pikvm/pikvm/docs/arduino_hid.md

!!! warning "Legacy warning"
    This page describes the legacy keyboard and mouse emulator used in old DIY builds.
    There is no point using it today because there is a more modern and better replacement for the [new Pico HID](pico_hid.md).
    This one can also serve as an in-place compatible replacement for the Arduino HID in the old build.

-----
## Serial HID

!!! warning "PiKVM V3 note"
    Use [the SPI HID](#spi-hid) for V3. Otherwise, you won't be able to use the Serial console.

### USB keyboard and mouse

1. ??? example "Get some parts"
    * Arduino Pro Micro (based on an ATMega32u4).
    * [Logic level shifter](https://www.sparkfun.com/products/12009).
    * 1x NPN transistor (almost any NPN transistor: 2n2222 or similar).
    * 1x 390 Ohm resistor.
    * A breadboard and wires.

2. ??? example "Build the Arduino HID according to the scheme"
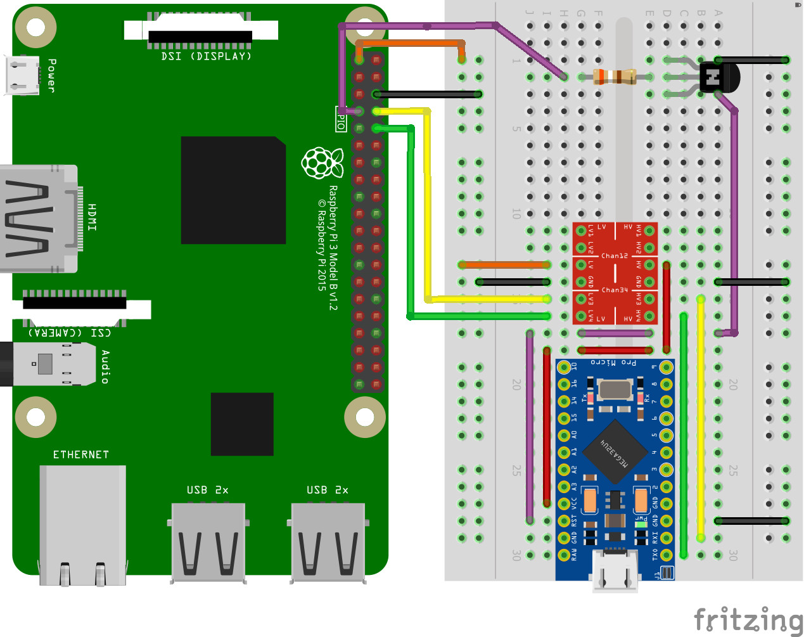
[picture p38: docs/arduino_hid/arduino_serial_hid.jpg]
    

3. Power up PiKVM and switch it to RW-mode using command `rw`.

4. Add these lines to `/etc/kvmd/override.yaml`:

    ```yaml
    kvmd:
        hid:
            type: serial
            reset_pin: 4
            device: /dev/kvmd-hid
    ```

5. Create file `/etc/udev/rules.d/99-kvmd-extra.rules`:

    ```udev
    KERNEL=="ttyAMA0", SYMLINK+="kvmd-hid"
    ```

6. Run `systemctl disable getty@ttyAMA0.service`.

7. Remove `console=ttyAMA0,115200`or `console=serial0,115200` and `kgdboc=ttyAMA0,115200` or `kgdboc=serial0,115200` from `/boot/cmdline.txt`.

8. [Flash the Arduino HID](flashing_hid.md).

9. Perform `reboot`.

### PS/2 keyboard

Using the PS/2 firmware currently have some limitations:

* The possibility of using the switchable USB HID is excluded.
* PS/2 mouse is not supported right now (but it will).

Both of these problems will be solved in the nearest future and the two different firmware versions will be combined into one universal one.

To select the PS/2 firmware, follow the instructions for the [USB](#usb-keyboard-and-mouse), but with one exception:

??? note "Before `make` you will need to edit file `platformio-avr.ini`"
    Open the file and find these lines:

    ```ini
    [_common]
    build_flags =
        -DHID_PS2_KBD_CLOCK_PIN=7
        -DHID_PS2_KBD_DATA_PIN=5
        -DHID_USB_CHECK_ENDPOINT
    # ----- The default config with dynamic switching -----
        -DHID_DYNAMIC
        -DHID_WITH_USB
        -DHID_SET_USB_KBD
        -DHID_SET_USB_MOUSE_ABS
    # ----- PS2 keyboard only -----
    #   -DHID_WITH_PS2
    #   -DHID_SET_PS2_KBD
    # ----- PS2 keyboard + USB absolute mouse -----
    #   -DHID_WITH_USB
    #   -DHID_WITH_PS2
    #   -DHID_SET_PS2_KBD
    #   -DHID_SET_USB_MOUSE_ABS
    # ----- PS2 keyboard + USB relative mouse -----
    #   -DHID_WITH_USB
    #   -DHID_WITH_PS2
    #   -DHID_SET_PS2_KBD
    #   -DHID_SET_USB_MOUSE_REL
    ```

    By default, the firmware works with USB HID and supports dynamic mode switching. You can choose one of the other modes by commenting some lines and uncommenting others. This example to use a USB mouse and PS/2 keyboard:

    ```ini
    ...
    # ----- The default config with dynamic switching -----
    #   -DHID_DYNAMIC
    #   -DHID_WITH_USB
    #   -DHID_SET_USB_KBD
    #   -DHID_SET_USB_MOUSE_ABS
    # ----- PS2 keyboard only -----
    ...
    # ----- PS2 keyboard + USB absolute mouse -----
        -DHID_WITH_USB
        -DHID_WITH_PS2
        -DHID_SET_PS2_KBD
        -DHID_SET_USB_MOUSE_ABS
    # ----- PS2 keyboard + USB relative mouse -----
    ...
    ```

Next, connect Arduino pins to the female PS/2 port of your motherboard. Choose the purple port. If your motherboard only have one port, it's probably universal and can be used either for the keyboard or for the mouse. Most likely, it is painted in two colors: green and purple. You can use it either.

??? example "Follow the diagram"
    | Female PS/2 port (front view) | Pinout |
    |-------------------------------|--------|
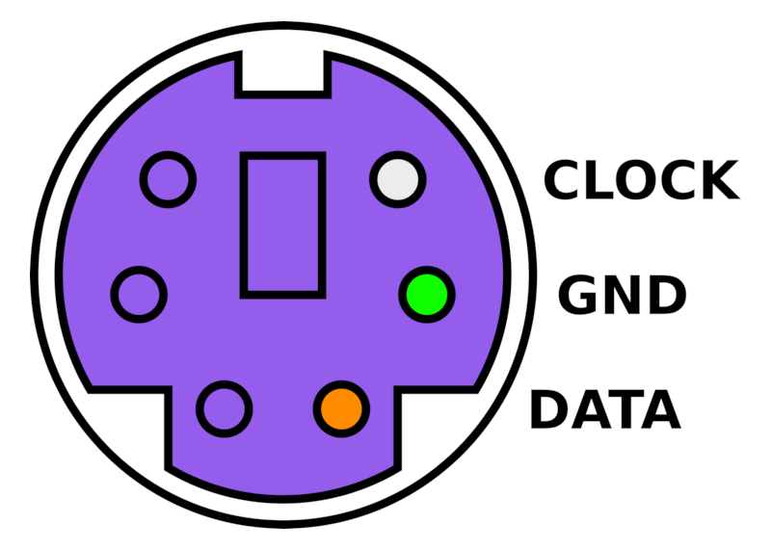
[picture p39: docs/arduino_hid/ps2_kbd.png]
    |  | Arduino pin 7 <-> PS/2 CLOCK<br>Arduino pin 5 <-> PS/2 DATA<br>Arduino GND pin <-> PS/2 GND |

    !!! warning
        Connect VIN pin of Arduino to [any Raspberry's 5v pin](https://pinout.xyz/pinout/5v_power) for PS/2 only device. But you don't need to connect the Arduino VIN pin if you connected USB (Arduino will get power through it).

-----
## SPI HID

Using an SPI connection, an Arduino Micro (not Pro) or compatible can be flashed from the Pi and used as an HID keyboard and mouse. Unlike UART, SPI does not share pins with Bluetooth on the Raspberry Pi so the Bluetooth radio does not need to be disabled.

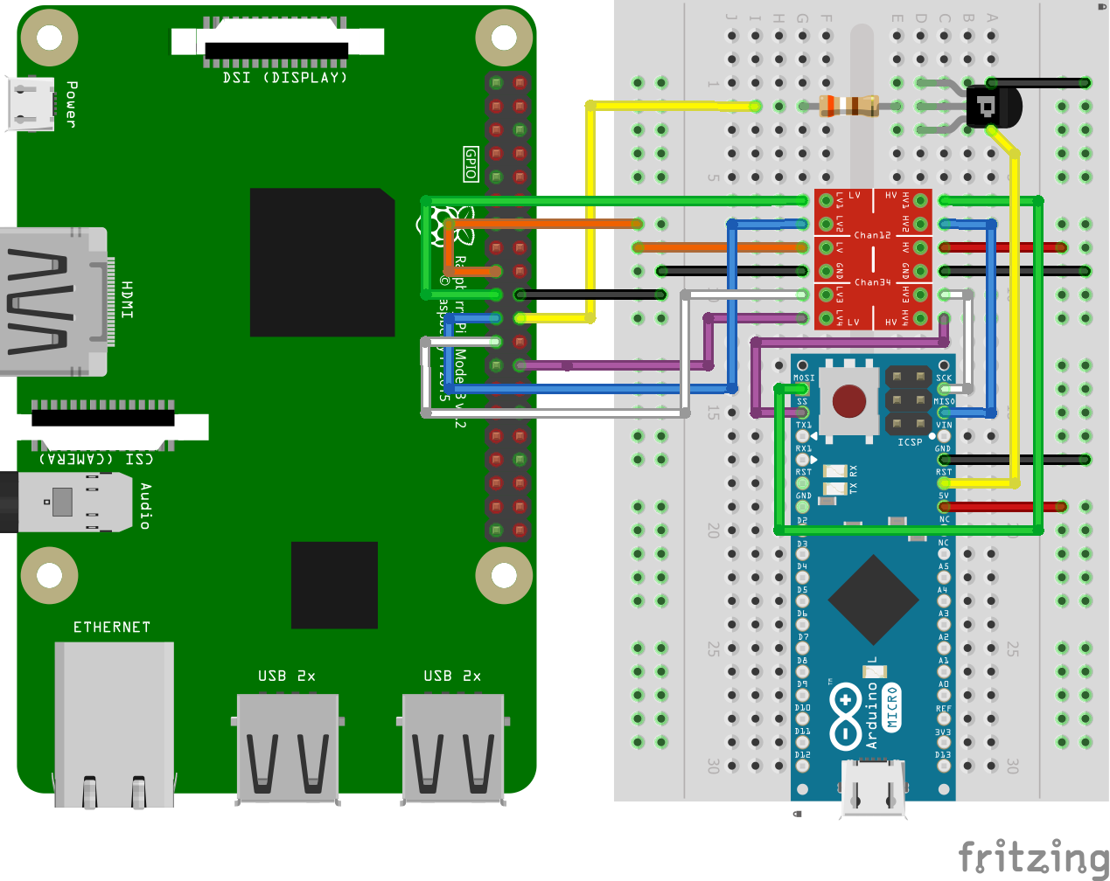
[picture p40: docs/arduino_hid/arduino_spi_hid.png]
Diagram of the Arduino SPI wiring for HID keyboard and mouse.


Before powering either device, double-check the connections. The following should be wired from the Pi to either the level shifter or the Arduino. While the Arduino tolerates 3.3V logic input, 5V outputs from the Arduino can damage or destroy the Raspberry Pi and must not be connected directly to 3.3V GPIO pins directly.

### Parts list

There are very few parts needed besides the Raspberry Pi to build the solution. Some parts may be purchased with or without headers, if headers are not pre-soldered, it may be necessary to order some breakaway header strips and solder them to the boards prior to assembly unless the wires will be soldered directly to the boards.

* Raspberry Pi Zero W or Pi 4 are the most popular boards for this solution, pre-soldered headers recommended
* Arduino Micro (or compatible) microcontroller board with pre-soldered headers recommended
* Logic Level Converter. This may be RX/TX, Bidirectional, or Single Supply
* 1x PNP transistor (2n2907 or equivalent).  Note this is different from the one suggested in the Serial HID docs above, that is an NPN while this is a PNP.
* 1x 390 ohm resistor
* Dupont wires (female to male pin) recommended for breadboard or other suitable means of making the connections
* *Optional:* Breakaway headers for the logic level converter
* *Optional:* Breadboard large enough to accommodate the parts
* *Optional:* Header pins for connection to a breadboard

!!! note
    A smaller "Pro Micro" board is available in a 3.3V model but the SS connection (RX_LED) is not available as a separate pin or solderable hole. If using this board, a jumper wire can be soldered to the resistor for the RX_LED but there is risk of burning the resistor, the LED, the board, or other components in the process. Advantages of this board include not requiring a logic level converter and reduced breadboard or board space for building the solution.

### List of connections to be made

For the primary functionality, most connections are made using a 4-channel bidirectional level shifter

* Pi 3v3 to LV on the level shifter
* Pi Ground to LV GND
* Arduino GND to HV GND
* GPIO10 (MOSI) via the level shifter to MOSI on the Arduino
* GPIO9 (MISO) via the level shifter to MISO on the Arduino
* GPIO11 (SPIO_SCLK) via the level shifter to SCK on the Arduino
* GPIO7 (SPIO_CE1_N) via the level shifter to SS (or RX_LED) on the Arduino

An additional circuit is used with a transistor to reset the HID for mode changes and for SPI programming as follows:

* GPIO25 to PNP base on transistor
* PNP emitter to ground
* PNP collector to  RST on the Arduino

Pictures of this setup are also available in full resolution for download to assist for both the Raspberry Pi and the Arduino board. A smaller version of the images has been included on this page and can be downloaded.

| Raspberry Pi Closeup | Breadboard with Arduino |
|---|---|
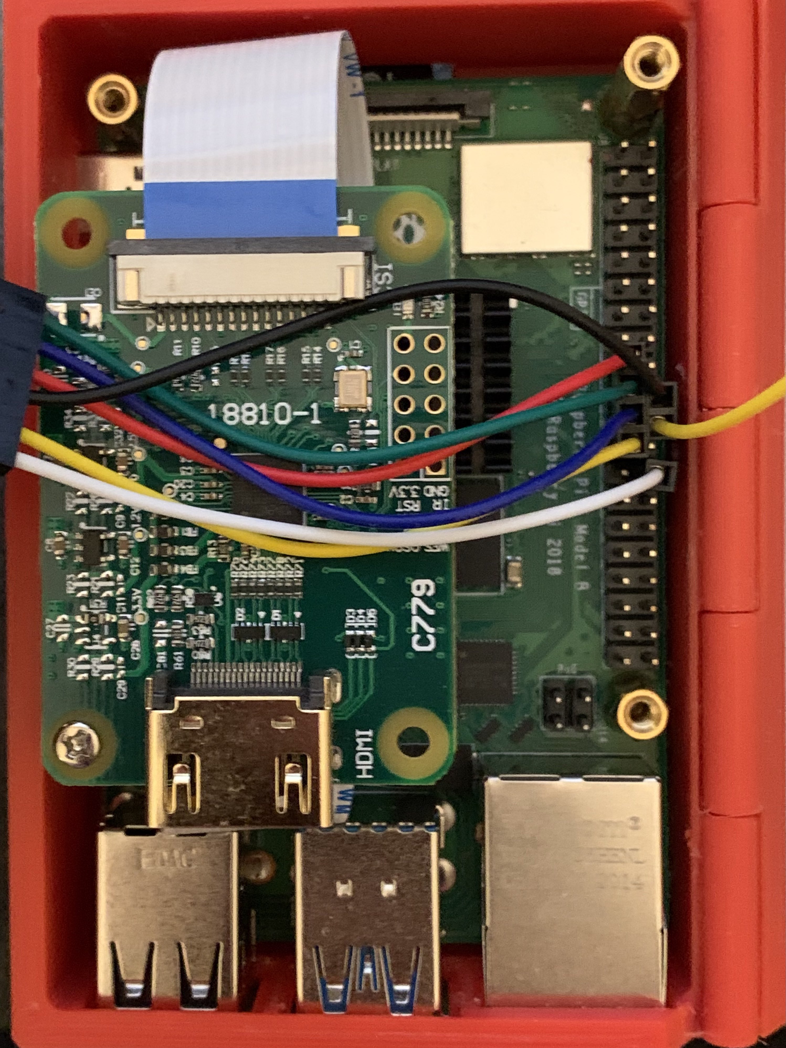
[picture p41: docs/arduino_hid/arduino_spi_hid_rpi.jpg]
A closeup of the Raspberry Pi wired to the breadboard.
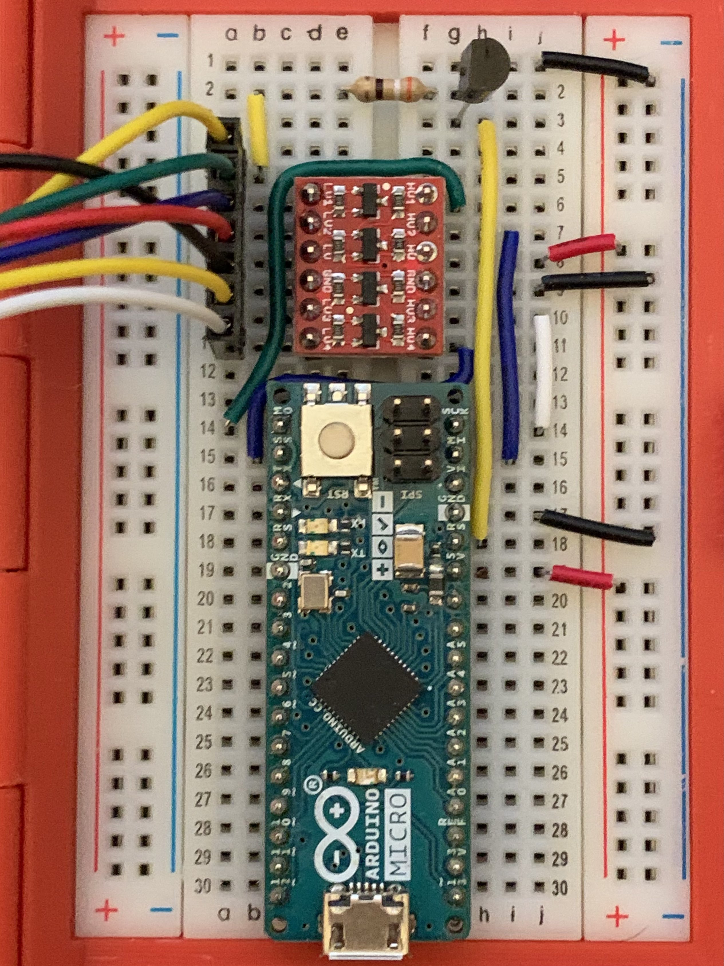
[picture p42: docs/arduino_hid/arduino_spi_hid_bb.jpg]
Arduino on a breadboard fully wired to the Pi.
|  |  |

Programming assumes the Arduino is powered via USB, either from the connected host or the Pi itself. If the USB is not connected, 5 V may be provided by the Raspberry Pi GPIO but should be disconnected prior to connecting USB to the Arduino's USB port. The Raspberry Pi does not have backcurrent protection, a circuit using one or more Schottky diodes can be built to OR power from multiple sources but it's easier and more cost effective to avoid conflict and voltage differences between power supplies by leaving the 5 V wire disconnected.

### Preparing the installation for SPI devices and programming

As of the latest package release, the kvmd service supports SPI. It should be sufficient to ensure the packages are up-to-date with the latest release, the programmer is installed, and the SPI device overlay is loaded at boot.

* Switch the filesystem to read-write mode with `rw`
* Add `dtoverlay=spi0-1cs` to `/boot/config.txt`
* Perform `reboot`.

### Flashing the Arduino

Instructions on flashing the Arduino can be found on the page [Flash the Arduino HID](flashing_hid.md).

If programming fails, ensure the Arduino is powered and check the wiring again. If there is a misconfiguration, power off the Pi and the Arduino, correct the wiring, and try again. Note it is not recommended or required to supply 5V power from the Raspberry Pi if the Arduino is USB powered, if the issue appears to be power related it may be removed from the solution and replaced with a powered USB connection if it will aid in troubleshooting but check all other wires first to ensure there are no shorts.

After you have double and triple-checked your wiring (in particular make sure the pins you are using on the Pi are correct, the documentation uses the GPIO pin labels, NOT the sequential pin numbers from 1-40. A good pinout reference is [@Gadgetoid's version](https://pinout.xyz/#), you might try flashing the Arduino by holding down the RESET button on the chip while running `make install`.  If this works, then at least you know your SPI wiring is correct.

Wiring problems are a common issue but there could be other reasons for programming not to complete. While it is not possible to list every possible problem and solution here, there is an active [user community](https://pikvm.org/support/) with others familiar with the solution and willing to help.

### Enable the SPI configuration and restart kvmd

Once the installation has completed, all that should remain is to add the following configuration to `/etc/kvmd/override.yaml` and restart the kvmd service. If the first line exists due to existing overrides, omit that line and either add or update the hid section as appropriate.

```yaml
kvmd:
    hid:
        type: spi
        chip: 0
        bus: 0
        sw_cs_pin: 7
        reset_pin: 25
        reset_inverted: true
```

After saving the changes to `/etc/kvmd/override.yaml`, restart `kvmd` and clear your browser cache. The command to restart `kvmd` is

```
# systemctl restart kvmd
```

If your device is still in read-write mode, `ro` will put the SD back in read-only mode.

-----
## Fixing the USB absolute mouse on Windows 98

Due to an ancient buggy driver, the USB absolute mouse on Windows 98 moves only within the upper-left quarter of the screen. To fix this, just recompile the firmware with uncommented flag `-DHID_WITH_USB_WIN98` in `platformio-avr.ini`.
