pikvm/pikvm/docs/blog/posts/2020/2020-08-02/index.md

---
title: "Ready-made images for Raspberry Pi4"
date: 2020-08-02
slug: ready-made-images-for-raspberry-pi4
description: >
      Now we provide the ready-made images for Raspberry Pi 4. You no longer need to build OS manually!
categories:
    - Products
authors:
    - mdevaev
links:
    - PiKVM: https://pikvm.org
    - Discord: https://discord.gg/bpmXfz
comments: true
---

The big update! Now we provide the ready-made images for Raspberry Pi 4. You no longer need to build OS manually!

<!-- more -->

You can flash the Pi-KVM OS to SD card under Linux, Mac, and Windows using the graphical installer.

Downloads are here: https://pikvm.org/download/.

The manual is here: https://docs.pikvm.org/flashing_os/.

Oh, and as you can see, now we have a small website: https://pikvm.org/. I would appreciate it if you share this link with your colleagues or friends in social networks.
