pikvm/pikvm/docs/index.md

---
title: PiKVM Handbook
description: Comprehensive guide to configuring and using your PiKVM
---

**Welcome to the [PiKVM](https://pikvm.org) Handbook**—a complete
documentation of the Open-Source KVM-over-IP on Raspberry Pi!

Here you will find comprehensive information about all aspects of the
operation of PiKVM, get answers to your most difficult questions and be
able to solve the problems that have arisen.

## Where to start?

* Check out the **device instructions**:

    {!_device_guides.md!}

* Learn about the **[basics of working with PiKVM](cheatsheet.md)**.

* **Explore the features of PiKVM** using the site's table of contents.

* **If you encounter a problem**, take a look at the **[FAQ](faq.md)**, but if nothing helped,
  feel free to contact our **[Support](https://pikvm.org/support/)** - many of experienced users and the PiKVM team will definitely help you.

## Links

* Website: **https://pikvm.org**
* GitHub: **https://github.com/pikvm**
* Discord: 
* Reddit: 
* [Forum](https://forum.pishop.com/c/pikvm)
