pikvm/pikvm/docs/blog/posts/2022/2022-06-09/index.md

---
title: "KVMD 3.101: PiKVM V3 + Audio = ❤️"
date: 2022-06-09
slug: kvmd-3-101-audio-on-pikvm-v3
description: >
    We are finally ready to provide audio for testing by all V3 users
categories:
    - Releases
authors:
    - mdevaev
links:
    - PiKVM: https://pikvm.org
    - Discord: https://discord.gg/bpmXfz5
    - KVMD release: https://github.com/pikvm/kvmd/releases/tag/v3.101
comments: true
---

This moment has come! We are finally ready to provide audio for testing by all V3 users. 

<!-- more -->

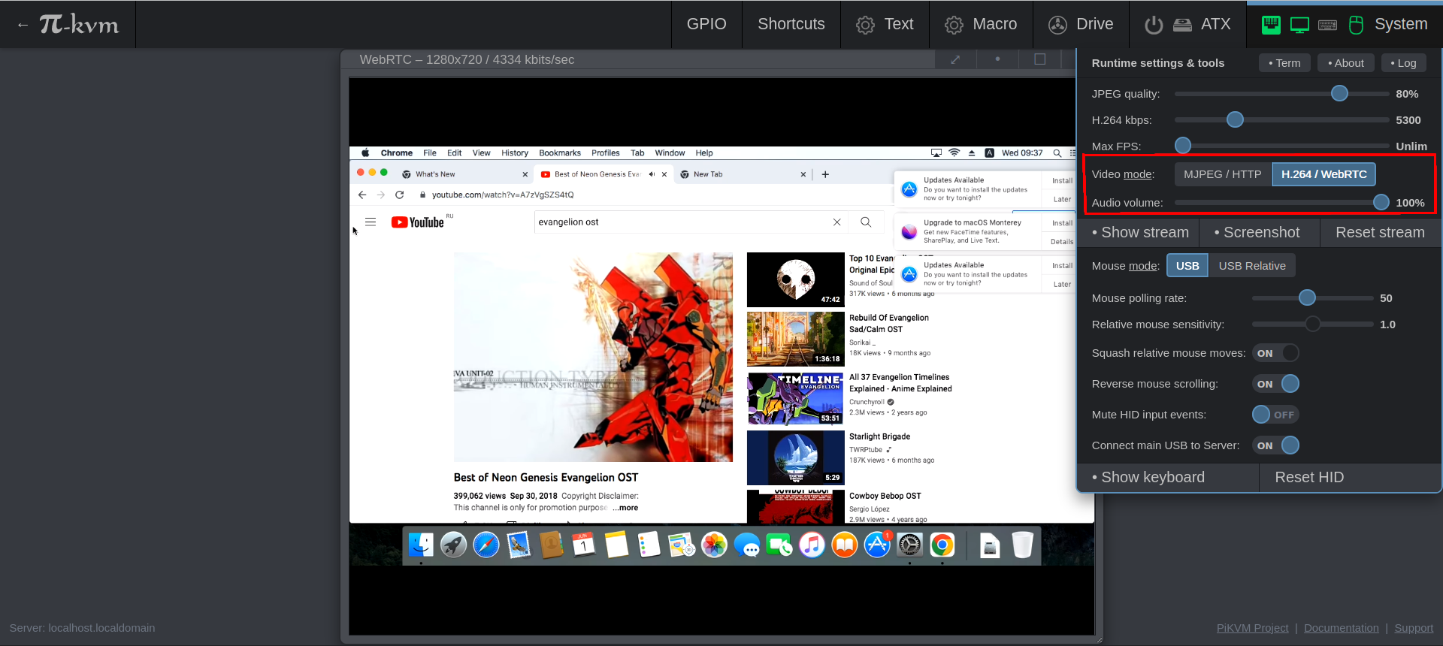
[picture p112: docs/blog/posts/2022/2022-06-09/pikvm-v3-audio.webp]
Audio on PiKVM v3


Right now everything is working pretty stable, so if you really wanted to watch a movie on KVM or something like that—this is your chance!

To start using audio, follow the simple instructions here: https://docs.pikvm.org/audio.
