pikvm/pikvm/docs/blog/posts/2024/2024-08-19/index.md

---
title: "KVMD 4.4: HDMI passthrough on V4 Plus is stable now"
date: 2024-08-19
slug: kvmd-4-4-stable-hdmi-passthrough-on-v4-plus
description: >
    Thanks to the work of the Raspberry kernel team, a bug related to incorrect colors in H.264 was finally fixed while working with passthrough
categories:
    - Products
authors:
    - mdevaev
links:
    - PiKVM: https://pikvm.org
    - Discord: https://discord.gg/bpmXfz5
    - KVMD release: https://github.com/pikvm/kvmd/releases/tag/v4.4
comments: true
---

Thanks to the work of the Raspberry kernel team, a bug related to incorrect colors in H.264 was finally fixed while working with passthrough.

<!-- more -->

With the new release, this feature is now enabled by default, and you will get great juicy colors both in the stream and on the external physical monitor. See [the documentation](https://docs.pikvm.org/pass) for details on setting this up.

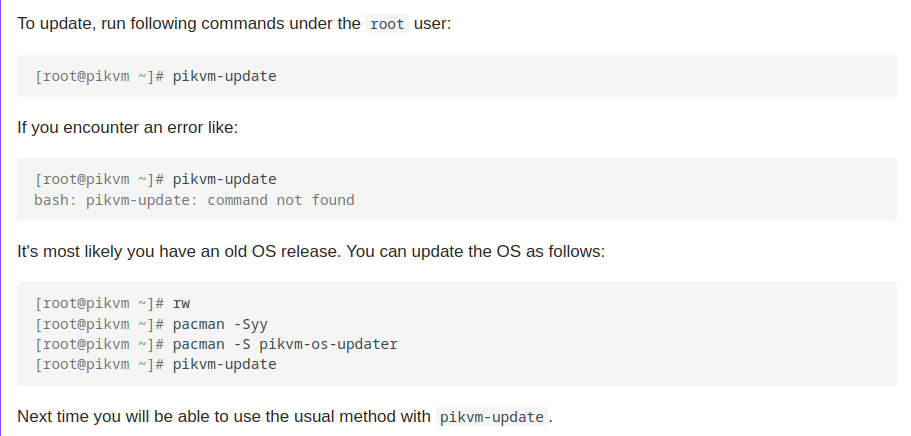
[picture p115: docs/blog/posts/2024/2024-08-19/pikvm-os-update.webp]
Updating PiKVM OS
