pikvm/pikvm/docs/blog/posts/2025/2025-01-24/index.md

---
title: "KVMD 4.49: DVD images support"
date: 2025-01-24
slug: kvmd-4-49-dvd-images-support
description: >
    Starting with KVMD 4.49, the old 2.2 GB CD limit was removed
categories:
    - Releases
authors:
    - mdevaev
links:
    - PiKVM: https://pikvm.org
    - Discord: https://discord.gg/bpmXfz5
    - KVMD release: https://github.com/pikvm/kvmd/releases/tag/v4.49
comments: true
---

Starting with KVMD 4.49, **the old 2.2 GB CD limit is now removed**.

<!-- more -->

PiKVM just learned how to support large DVD images natively, which means that **you no longer need Ventoy to prepare Flash images for PiKVM**. You can even use the official Windows ISO to install the OS! Small ISO images will be handled as CD as before, but for big images PiKVM will switch emulation to DVD mode automatically.

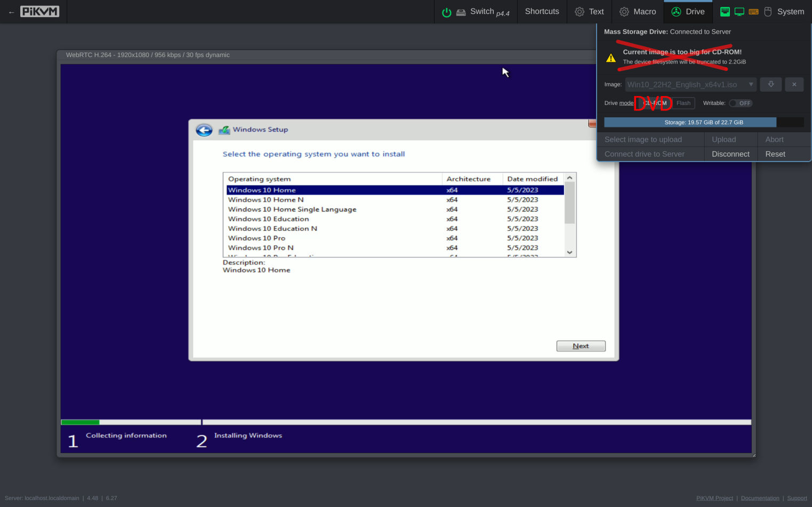
[picture p117: docs/blog/posts/2025/2025-01-24/no-cd-iso-limit.webp]
No CD ISO limit


How to update: `pikvm-update`, as usual.

If you've been dreaming of getting DVD emulation, then your wish has been fulfilled 🙂
