pikvm/pikvm/docs/blog/posts/2025/2025-05-27/index.md

---
title: "KVMD 4.76: Advanced diagnostics for the video stream"
date: 2025-05-27
slug: kvmd-4-76-advanced-diagnostics-for-the-video-streams
description: >
    Now you will see the reason why there is no signal
categories:
    - Releases
authors:
    - mdevaev
links:
    - PiKVM: https://pikvm.org
    - Discord: https://discord.gg/bpmXfz5
    - KVMD release: https://github.com/pikvm/kvmd/releases/tag/v4.76
comments: true
---

Now you will see the reason why there is no signal. We reliably distinguish the condition of the cable from the absence of a signal or unsupported video mode.

<!-- more -->

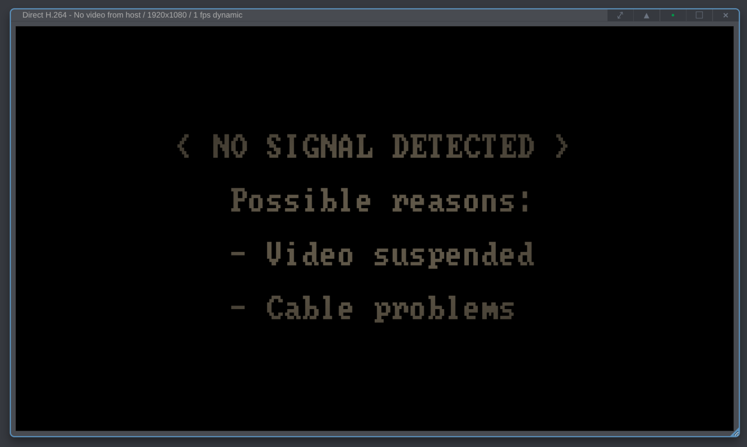
[picture p118: docs/blog/posts/2025/2025-05-27/video-stream-diagnostics.webp]
Video stream diagnostics
