pikvm/pikvm/docs/switch/switch_back.jpg

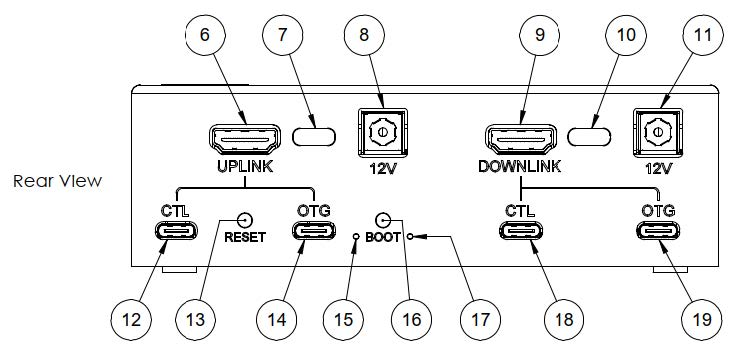
docs/switch/switch_back.jpg
