pikvm/pikvm/docs/switch/switch_back_blank.jpg

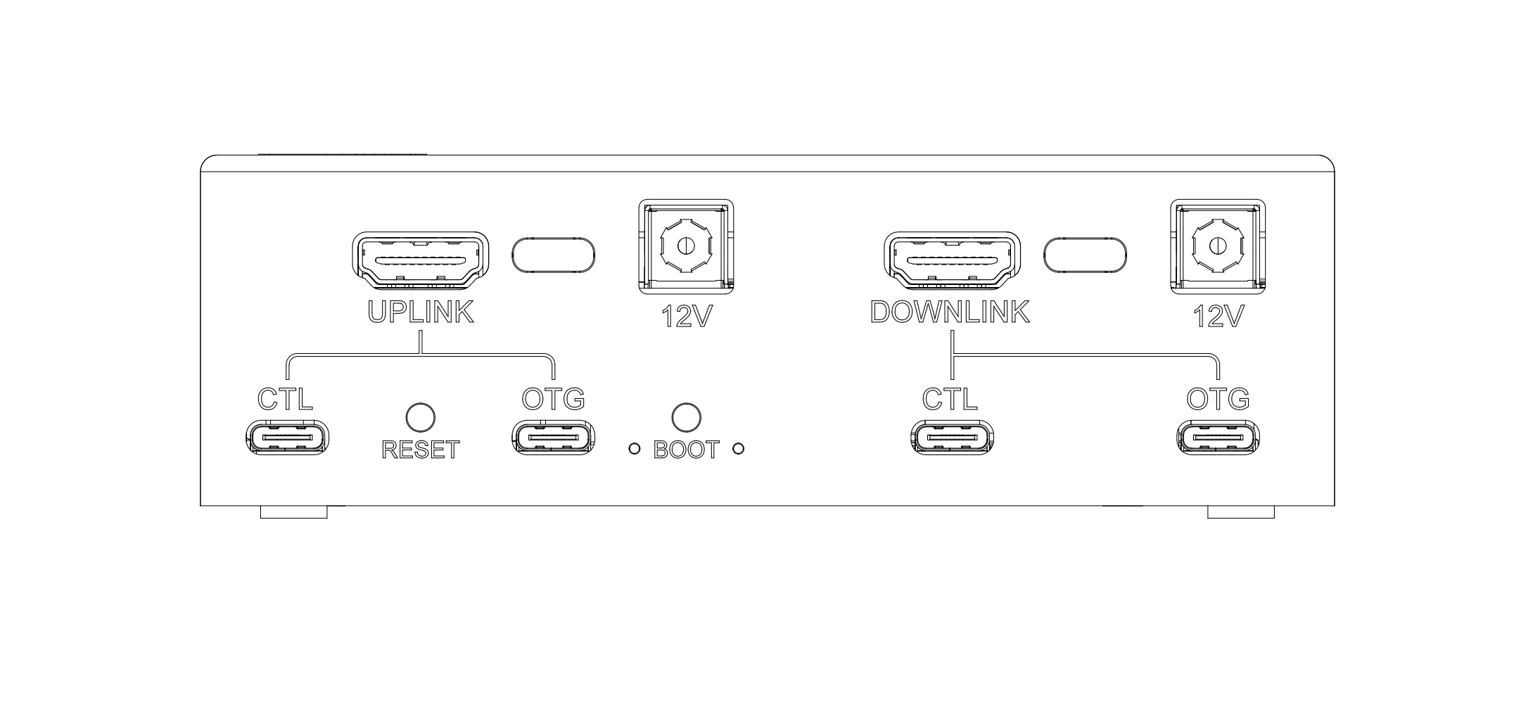
docs/switch/switch_back_blank.jpg
