pikvm/pikvm/docs/switch/switch_front.jpg

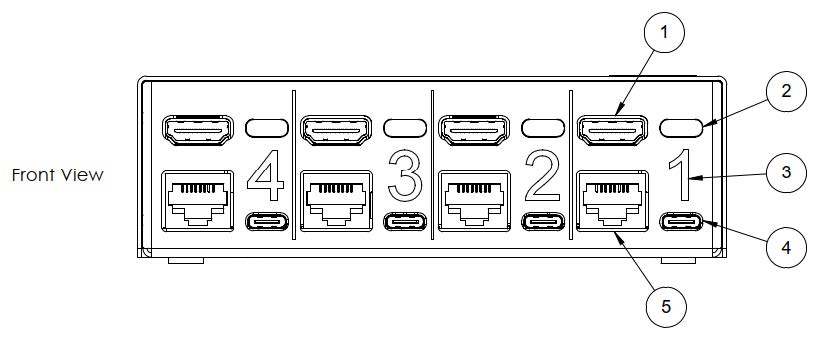
docs/switch/switch_front.jpg
