pikvm/pikvm/docs/switch/switch_front_blank.jpg

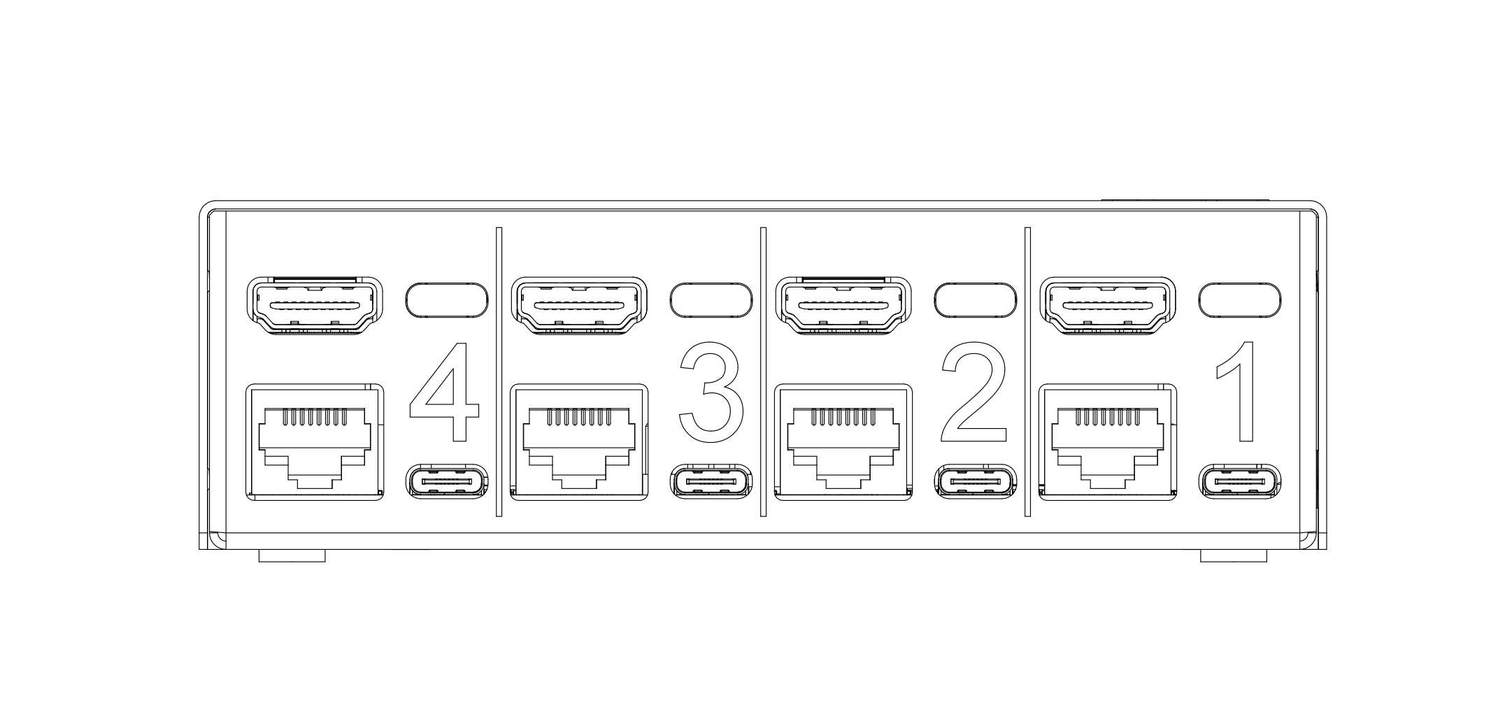
docs/switch/switch_front_blank.jpg
