pikvm/pikvm/docs/switch/v4plus_back.jpg

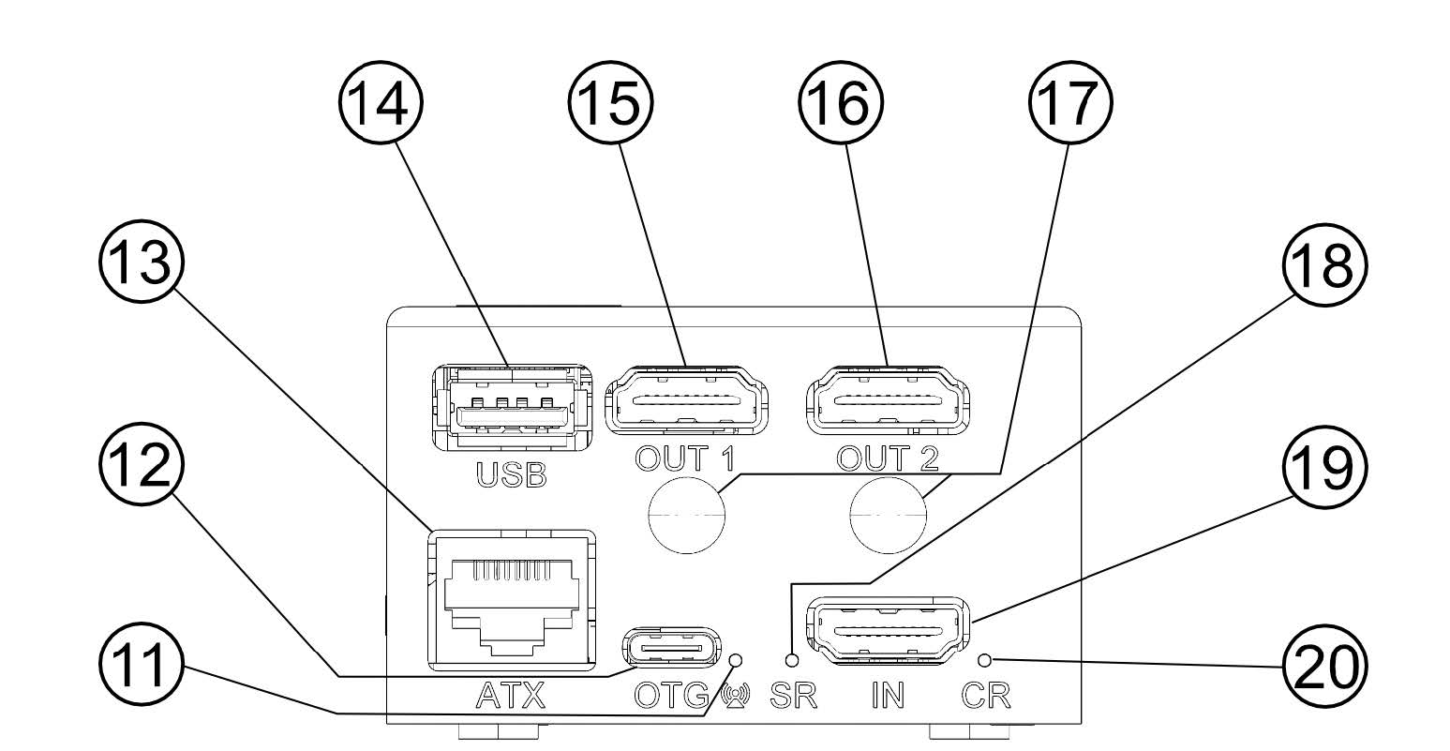
docs/switch/v4plus_back.jpg
