pikvm/pikvm/docs/switch/v4plus_front.jpg

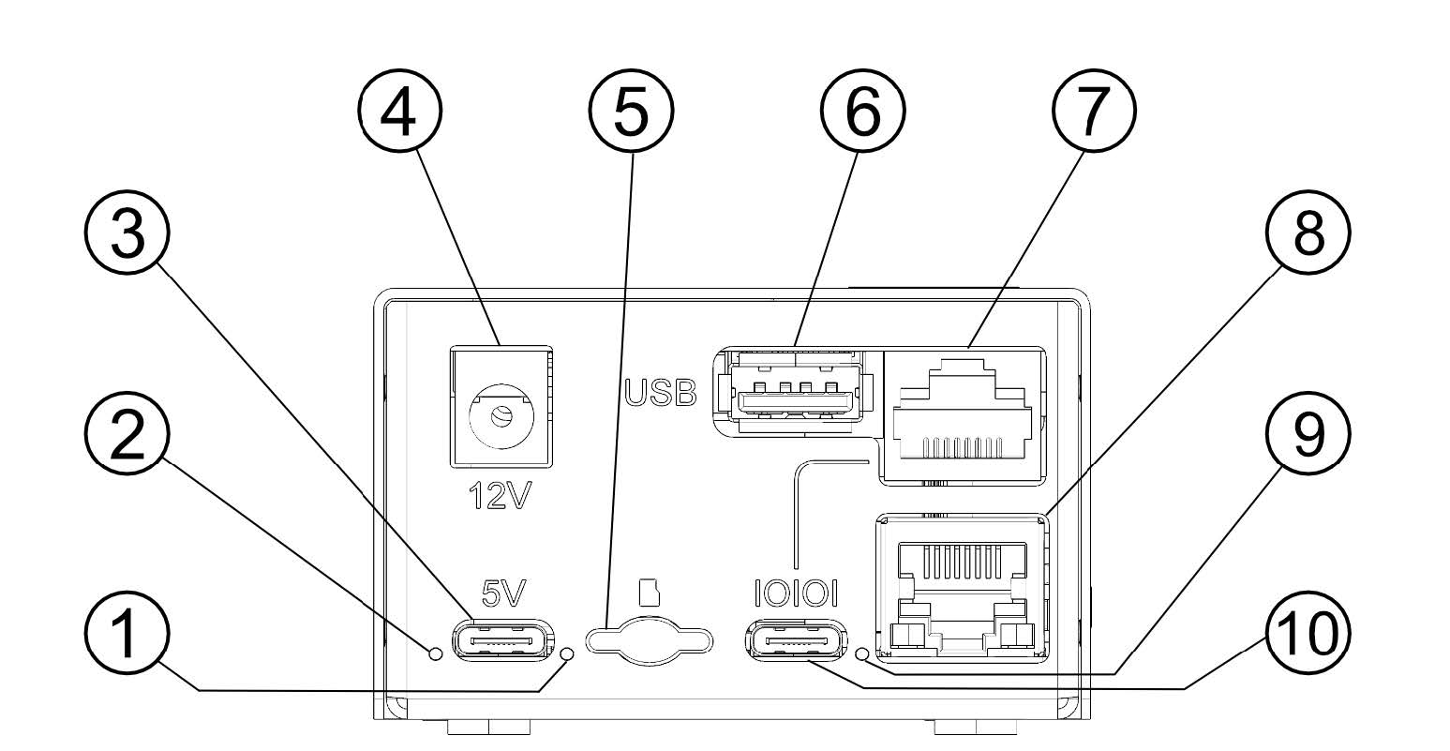
docs/switch/v4plus_front.jpg
