pikvm/pikvm/docs/v4/in-the-box.jpg

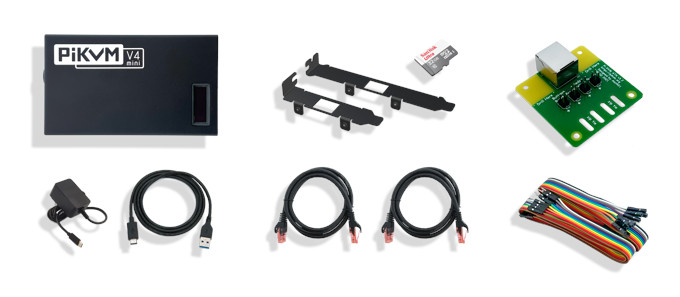
docs/v4/in-the-box.jpg
