pikvm/pikvm/docs/v4/plus_back.jpg

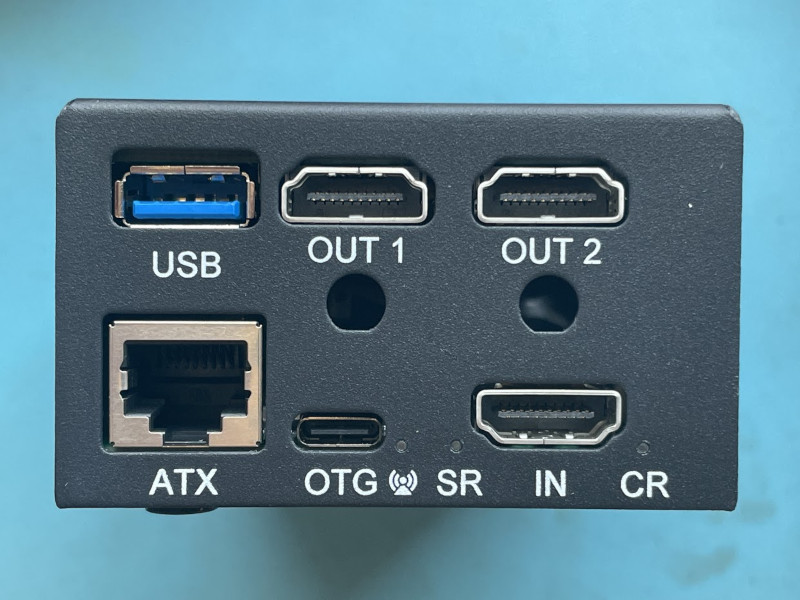
docs/v4/plus_back.jpg
