pikvm/pikvm/docs/v4/plus_front.jpg

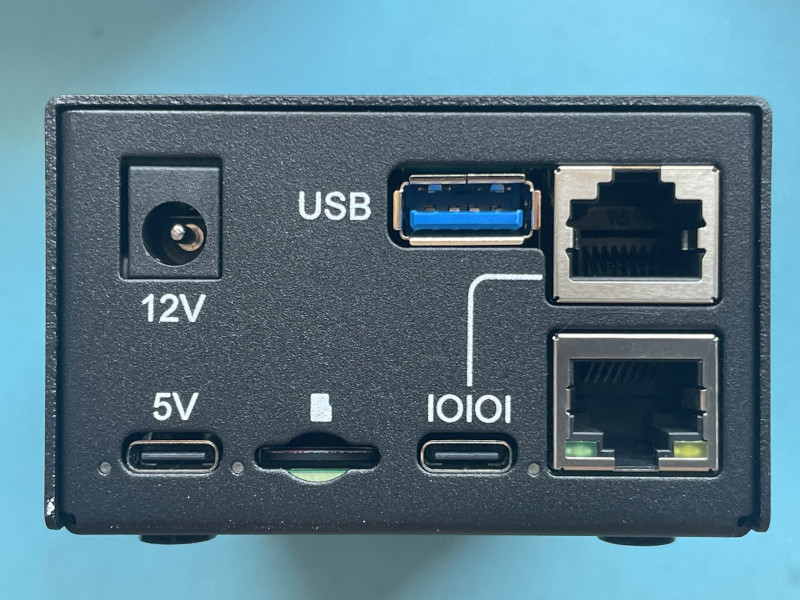
docs/v4/plus_front.jpg
