pikvm/pikvm/docs/v4/plus_right.jpg

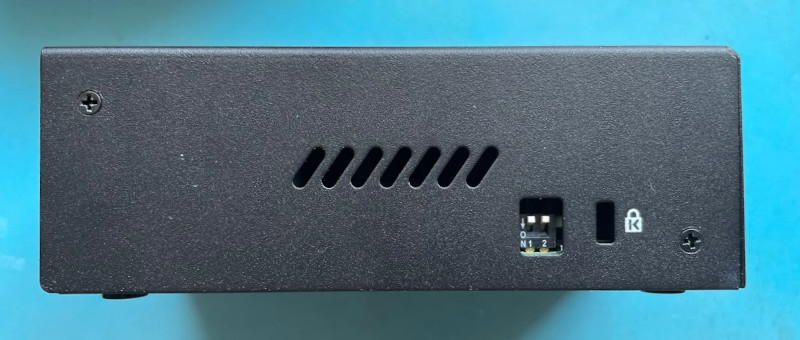
docs/v4/plus_right.jpg
