pikvm/pikvm/docs/v4/v4_dip_switches.png

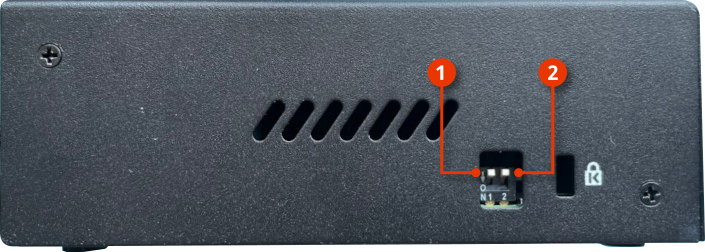
docs/v4/v4_dip_switches.png
