pikvm/pikvm/docs/video/menu.png

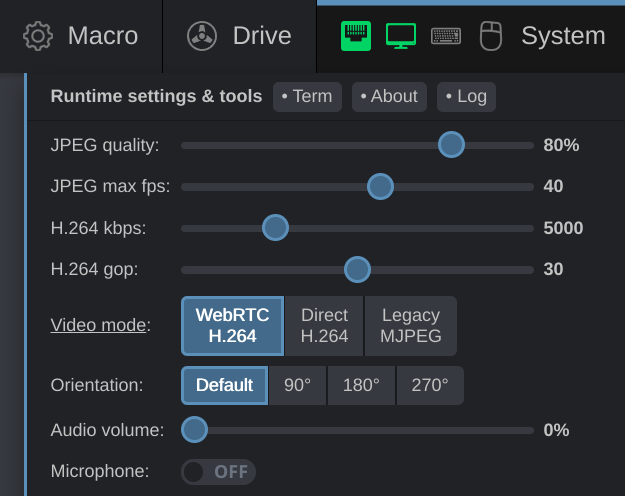
docs/video/menu.png
