pikvm/pikvm/img/v3_board.jpg

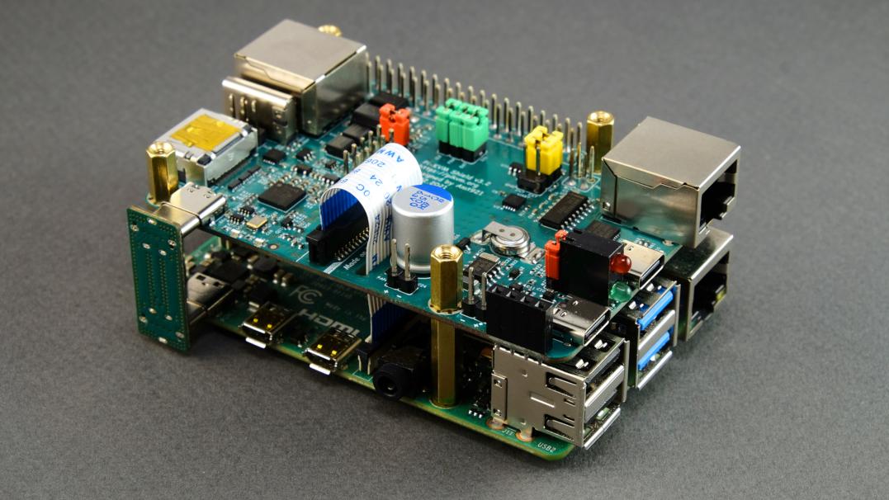
img/v3_board.jpg
