pikvm/pikvm/img/v3_kit.jpg

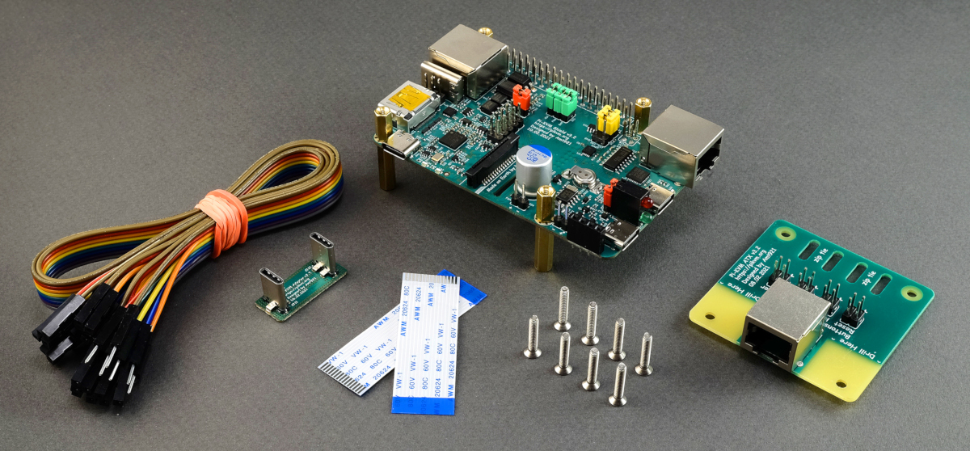
img/v3_kit.jpg
